chicco83/CHIRON-EVO/CHIRON/MOD HARDWARE/Anycubic_Trigorilla_stepper_driver_cooling_tunnel/images/3d06d213e04ff6a96ca5a01eb243599f_preview_featured.jpg

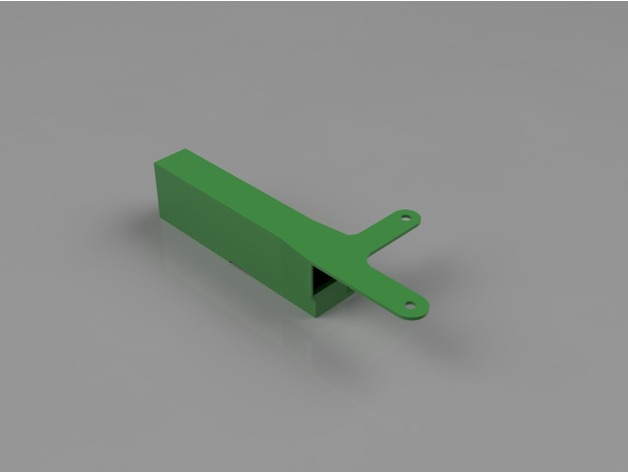
CHIRON/MOD HARDWARE/Anycubic_Trigorilla_stepper_driver_cooling_tunnel/images/3d06d213e04ff6a96ca5a01eb243599f_preview_featured.jpg
