chicco83/CHIRON-EVO/CHIRON/MOD HARDWARE/Anycubic_Trigorilla_stepper_driver_cooling_tunnel/images/8a05004b01cabfccfdbc358d301da0ce_preview_featured.jpg

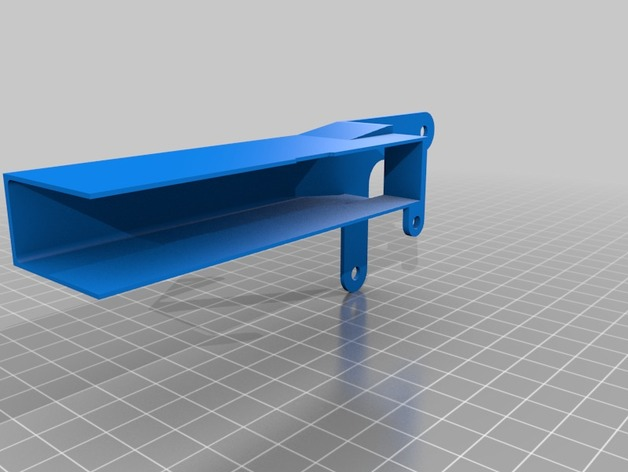
CHIRON/MOD HARDWARE/Anycubic_Trigorilla_stepper_driver_cooling_tunnel/images/8a05004b01cabfccfdbc358d301da0ce_preview_featured.jpg
