chicco83/CHIRON-EVO/CHIRON/MOD HARDWARE/Anycubic_Trigorilla_stepper_driver_cooling_tunnel/images/15cb524d84b9f957b413cb026b615ea2_preview_featured.jpg

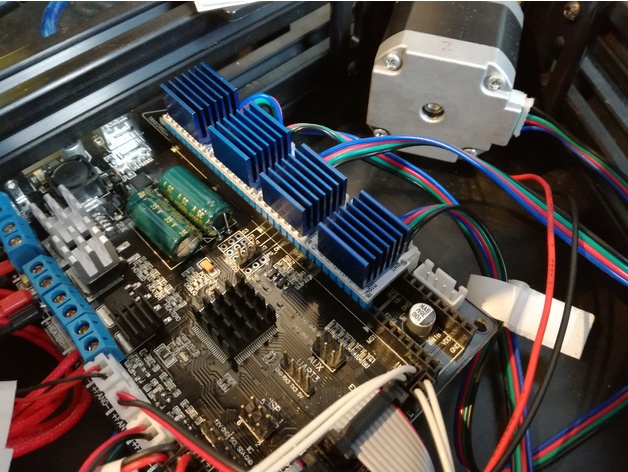
CHIRON/MOD HARDWARE/Anycubic_Trigorilla_stepper_driver_cooling_tunnel/images/15cb524d84b9f957b413cb026b615ea2_preview_featured.jpg
