chicco83/CHIRON-EVO/CHIRON/MOD HARDWARE/Anycubic_Trigorilla_stepper_driver_cooling_tunnel/images/66a94cb5b75e74bb501bde0653936604_preview_featured.jpg

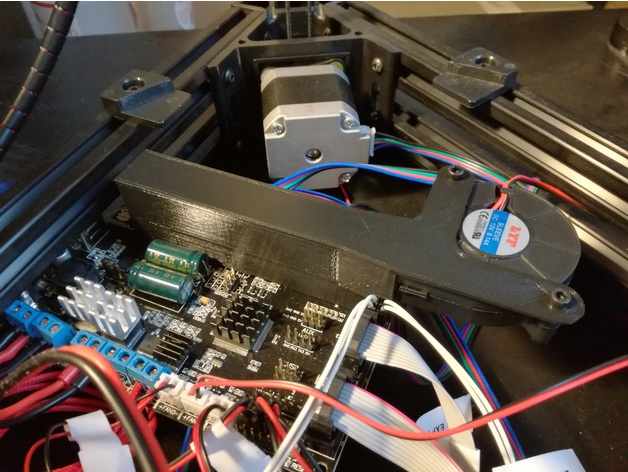
CHIRON/MOD HARDWARE/Anycubic_Trigorilla_stepper_driver_cooling_tunnel/images/66a94cb5b75e74bb501bde0653936604_preview_featured.jpg
