chicco83/CHIRON-EVO/CHIRON/MOD HARDWARE/Anycubic_Trigorilla_stepper_driver_cooling_tunnel/images/ea7234caf57d9d8a31c44bf39c441c15_preview_featured.jpg

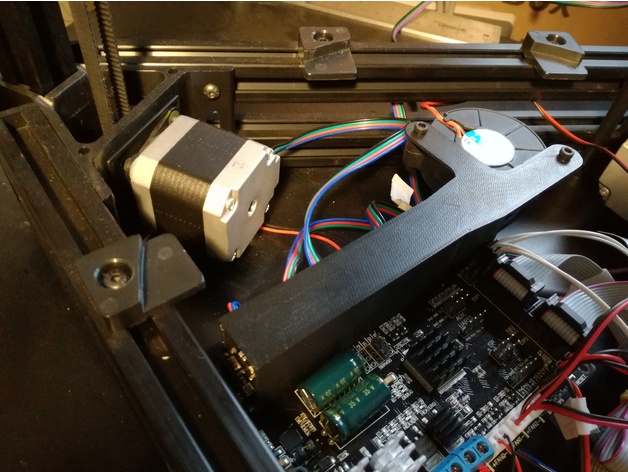
CHIRON/MOD HARDWARE/Anycubic_Trigorilla_stepper_driver_cooling_tunnel/images/ea7234caf57d9d8a31c44bf39c441c15_preview_featured.jpg
