chicco83/CHIRON-EVO/CHIRON/MOD HARDWARE/Anycubic_Trigorilla_stepper_driver_cooling_tunnel/images/ef3686a6fdcb9c2ef37c34229aa68580_preview_featured.jpg

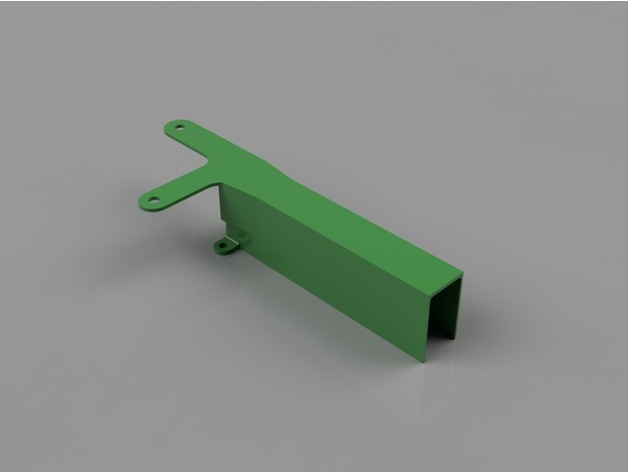
CHIRON/MOD HARDWARE/Anycubic_Trigorilla_stepper_driver_cooling_tunnel/images/ef3686a6fdcb9c2ef37c34229aa68580_preview_featured.jpg
