chicco83/CHIRON-EVO/CHIRON/MOD HARDWARE/Anycubic_Trigorilla_stepper_driver_cooling_tunnel/images/f9e21edd439fd3e9c4fc6578d0b51568_preview_featured.jpg

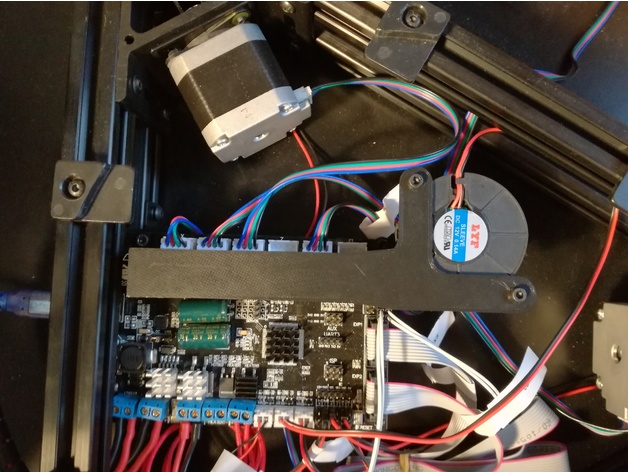
CHIRON/MOD HARDWARE/Anycubic_Trigorilla_stepper_driver_cooling_tunnel/images/f9e21edd439fd3e9c4fc6578d0b51568_preview_featured.jpg
