chicco83/CHIRON-EVO/CHIRON/MOD HARDWARE/PANNELLO PULSANTI/Octoprint+Buttonbox+/files/IMG_20211204_123243.jpg

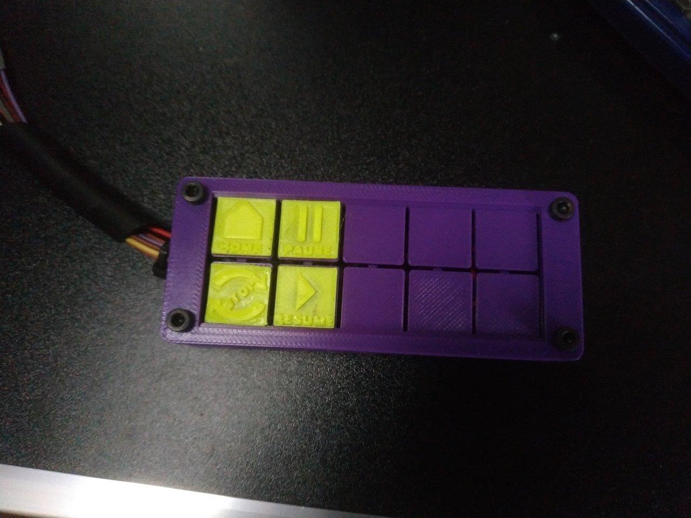
CHIRON/MOD HARDWARE/PANNELLO PULSANTI/Octoprint+Buttonbox+/files/IMG_20211204_123243.jpg
