chicco83/CHIRON-EVO/CHIRON/MOD HARDWARE/PANNELLO PULSANTI/Octoprint+Buttonbox+/images/20200816_074949-2.jpg

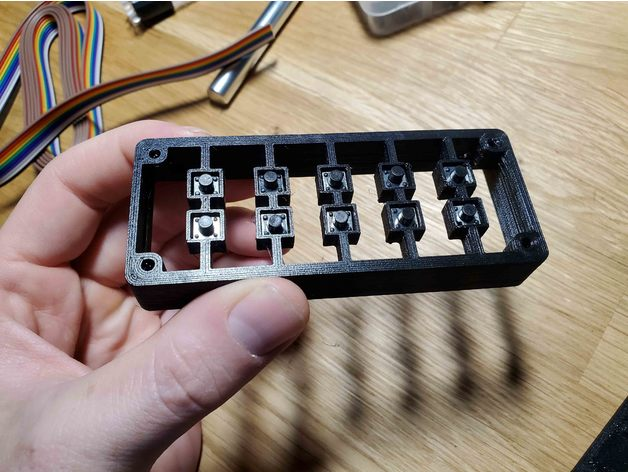
CHIRON/MOD HARDWARE/PANNELLO PULSANTI/Octoprint+Buttonbox+/images/20200816_074949-2.jpg
