chicco83/CHIRON-EVO/CHIRON/MOD HARDWARE/PANNELLO PULSANTI/Octoprint+Buttonbox+/images/20200816_090715.jpg

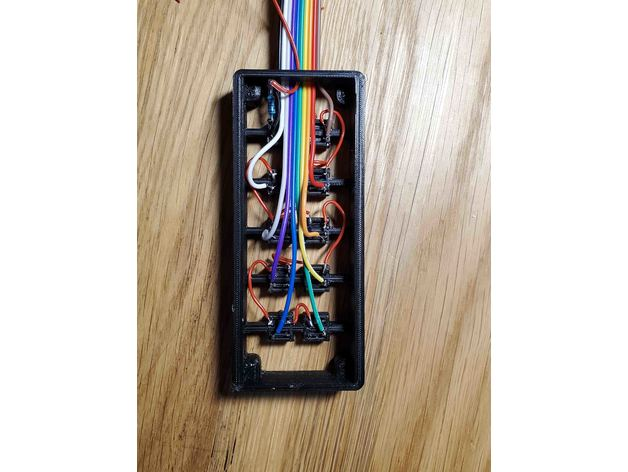
CHIRON/MOD HARDWARE/PANNELLO PULSANTI/Octoprint+Buttonbox+/images/20200816_090715.jpg
