chicco83/CHIRON-EVO/CHIRON/MOD HARDWARE/pinout cavo nero.jpg

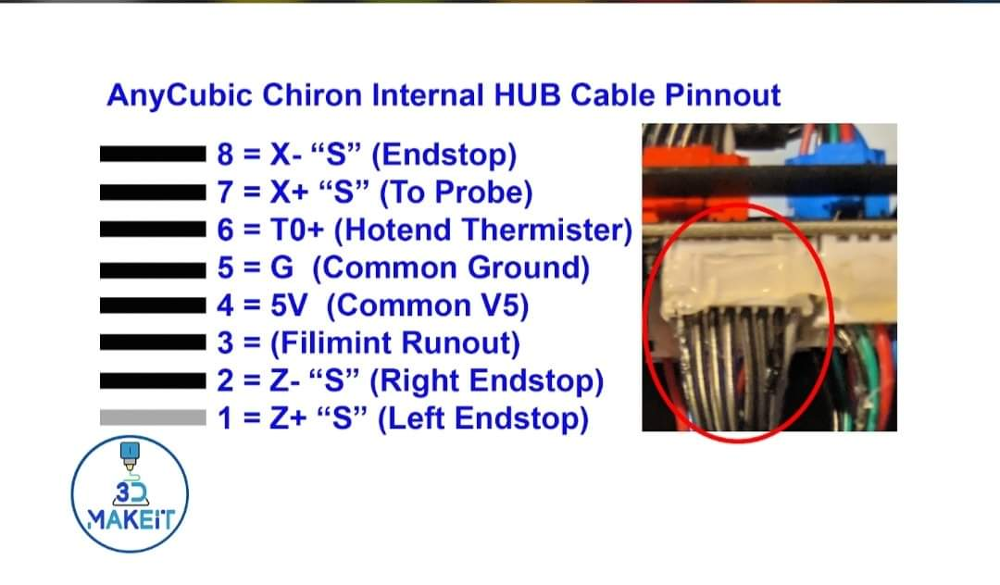
CHIRON/MOD HARDWARE/pinout cavo nero.jpg
