chicco83/CHIRON-EVO/CHIRON/MOD HARDWARE/PINOUT CONNETTORE ROSSO ESTRUSORE.jpg

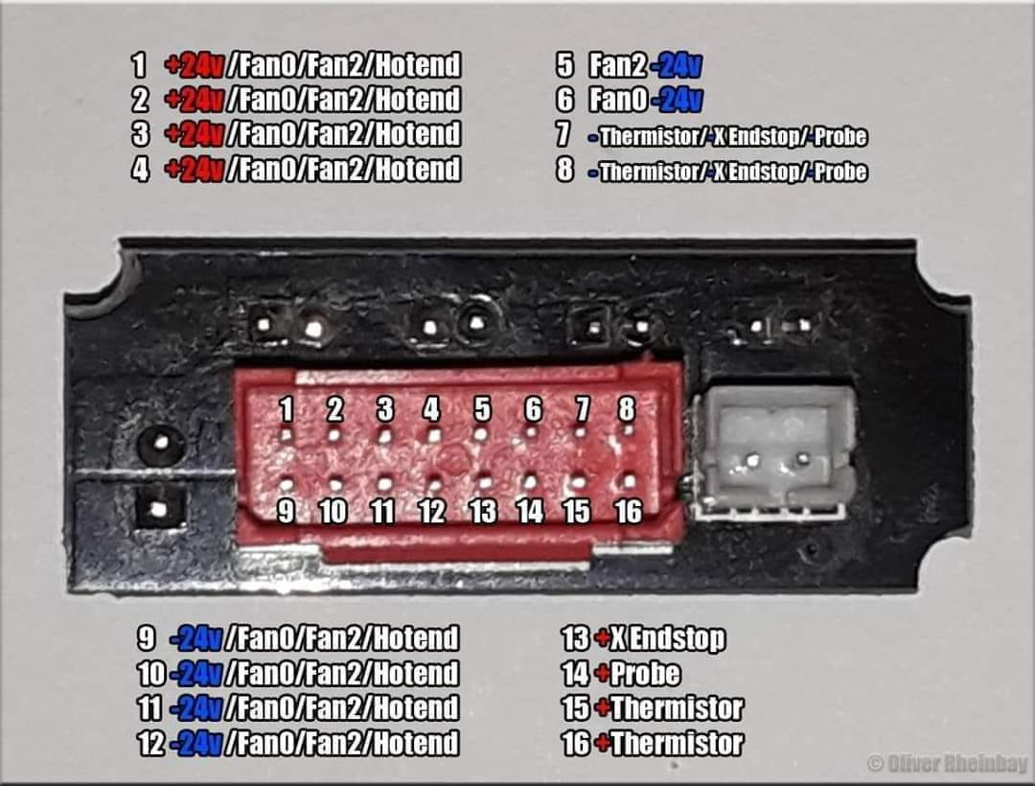
CHIRON/MOD HARDWARE/PINOUT CONNETTORE ROSSO ESTRUSORE.jpg
