chicco83/CHIRON-EVO/CHIRON/MOD HARDWARE/Supporto Stabilizzante Chiron/Images/Componente top Chiron.PNG

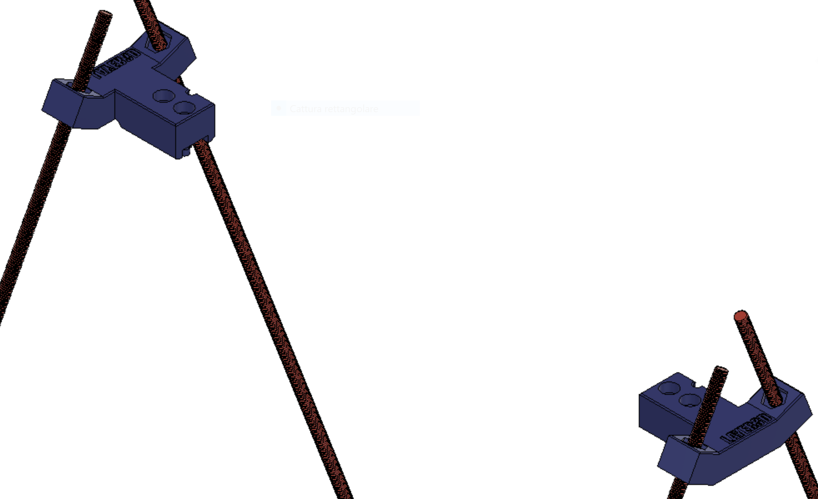
CHIRON/MOD HARDWARE/Supporto Stabilizzante Chiron/Images/Componente top Chiron.PNG
