chicco83/CHIRON-EVO/CHIRON/MOD HARDWARE/Supporto Stabilizzante Chiron/Images/Piedi scarico tensioni Z Chiron.PNG

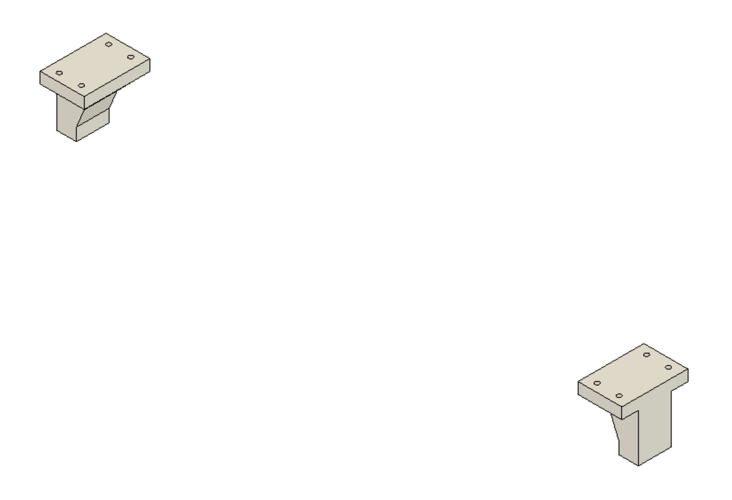
CHIRON/MOD HARDWARE/Supporto Stabilizzante Chiron/Images/Piedi scarico tensioni Z Chiron.PNG
