chicco83/CHIRON-EVO/CHIRON/MOD HARDWARE/Supporto Stabilizzante Chiron/Images/Rinforzo asse y Chiron.PNG

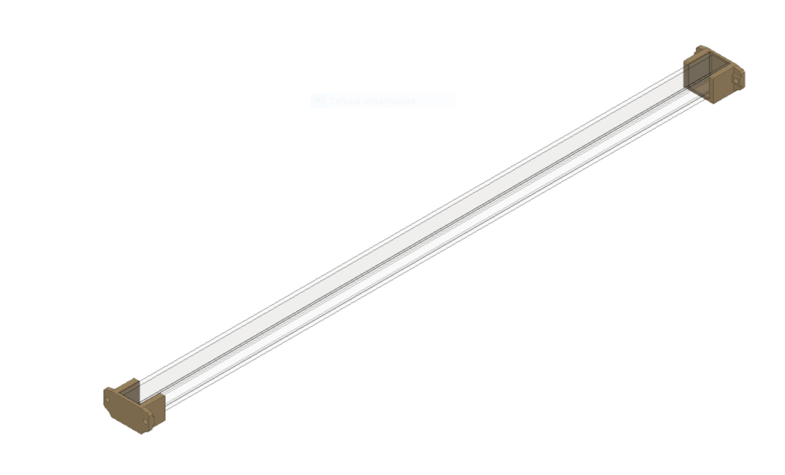
CHIRON/MOD HARDWARE/Supporto Stabilizzante Chiron/Images/Rinforzo asse y Chiron.PNG
