chicco83/CHIRON-EVO/CHIRON/MOD HARDWARE/trigorilla_motherboard_pinout.jpg

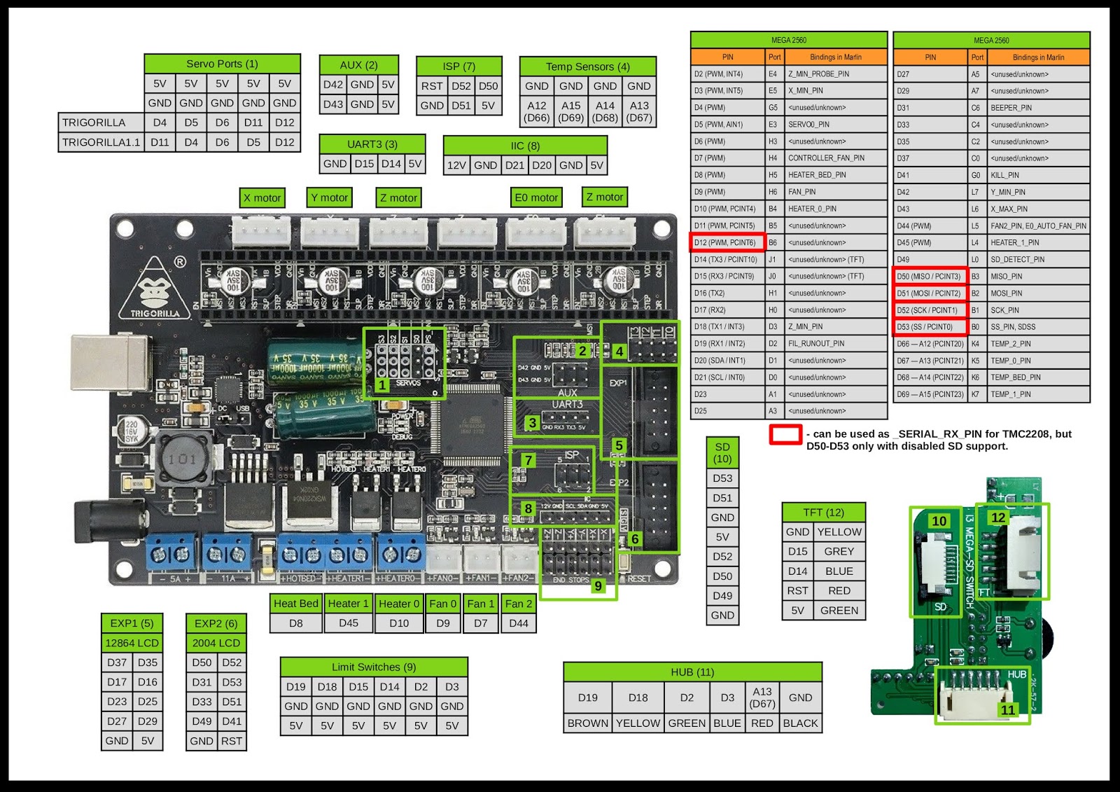
CHIRON/MOD HARDWARE/trigorilla_motherboard_pinout.jpg
