chicco83/CHIRON-EVO/CHIRON/SUPERSLICER/CHIRON BED.png

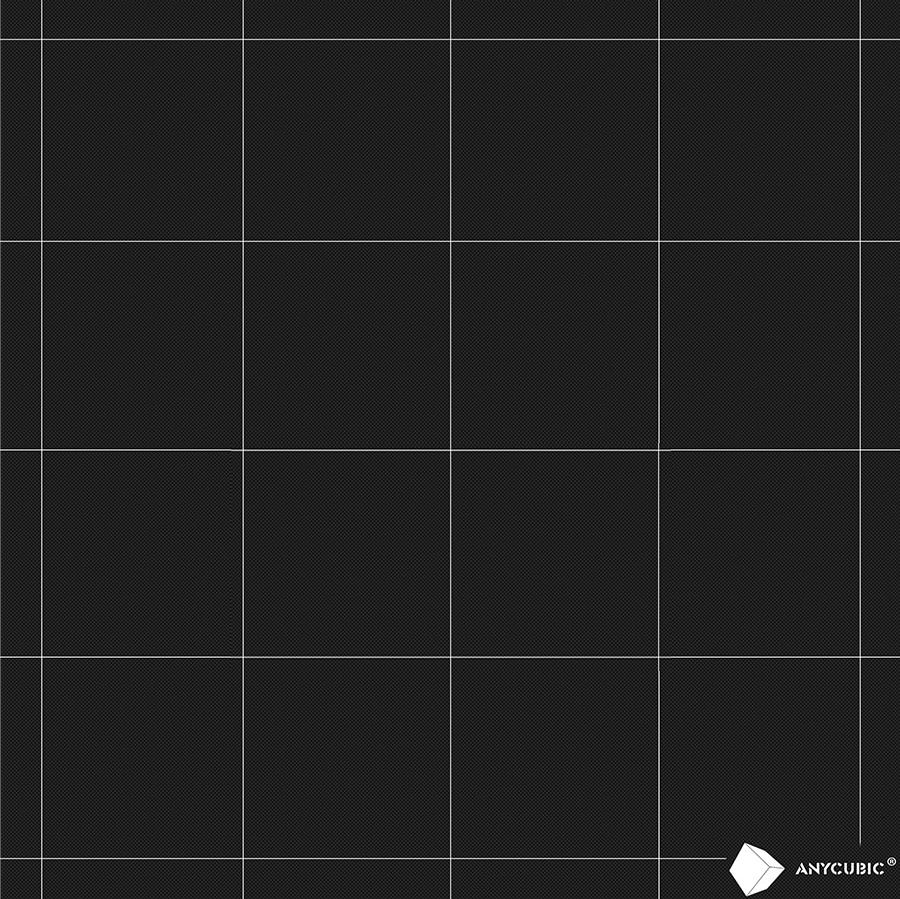
CHIRON/SUPERSLICER/CHIRON BED.png
