chicco83/CHIRON-EVO/CHIRON/VREF/Anycubic Chiron Vrefs.png

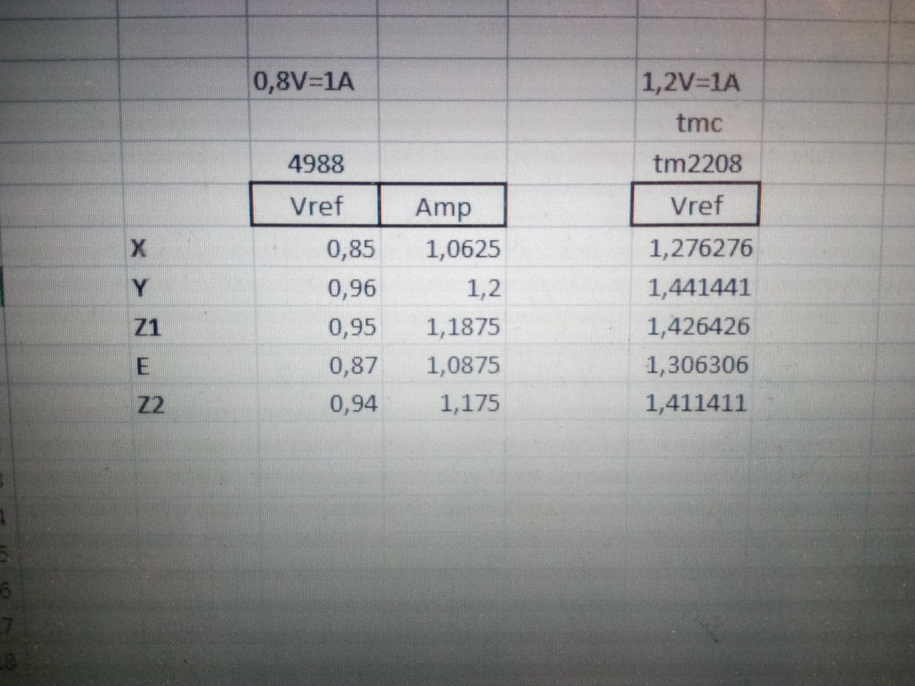
CHIRON/VREF/Anycubic Chiron Vrefs.png
