chicco83/CHIRON-EVO/CHIRON/VREF/vref anycubic - credit gruppo fb chiron italia/FB_IMG_1618653829422.jpg

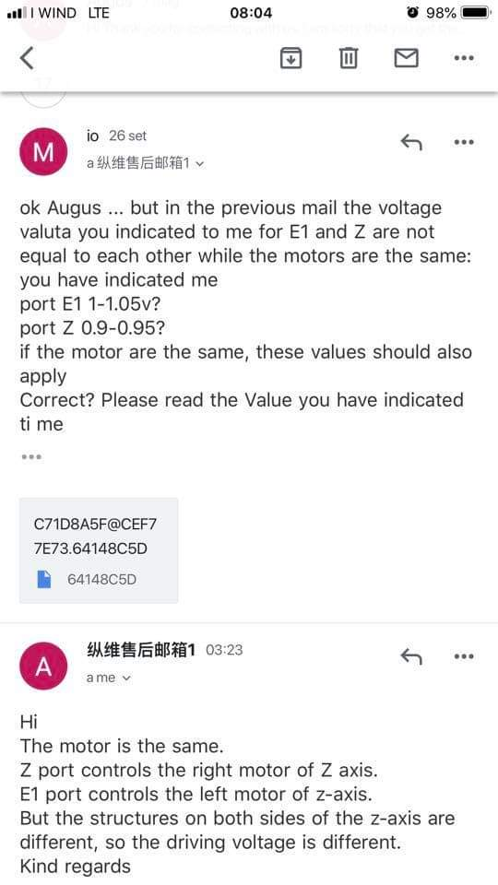
CHIRON/VREF/vref anycubic - credit gruppo fb chiron italia/FB_IMG_1618653829422.jpg
