chicco83/CHIRON-EVO/KLIPPER/DA STAMPARE/5v relay case/images/5V_relay_v2.jpg

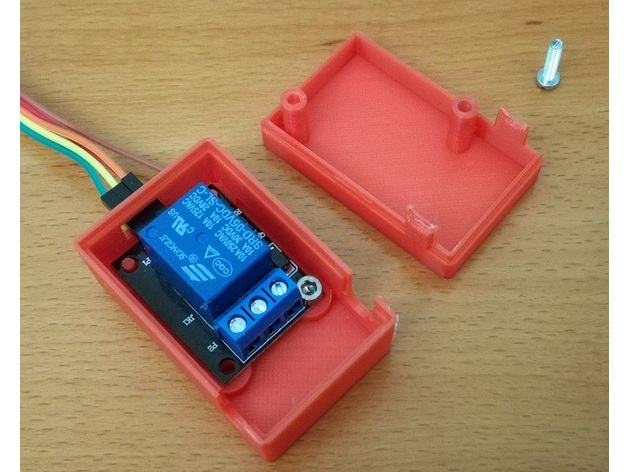
KLIPPER/DA STAMPARE/5v relay case/images/5V_relay_v2.jpg
