chicco83/CHIRON-EVO/KLIPPER/DA STAMPARE/5v relay case/images/extension_cord.jpg

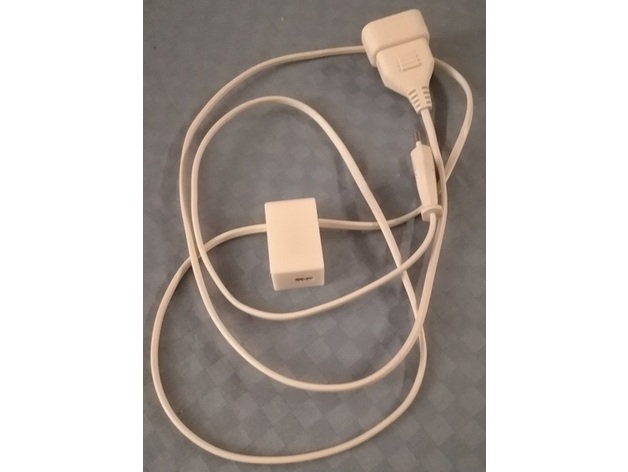
KLIPPER/DA STAMPARE/5v relay case/images/extension_cord.jpg
