chicco83/CHIRON-EVO/KLIPPER/DA STAMPARE/5v relay case/images/Parameters.jpg

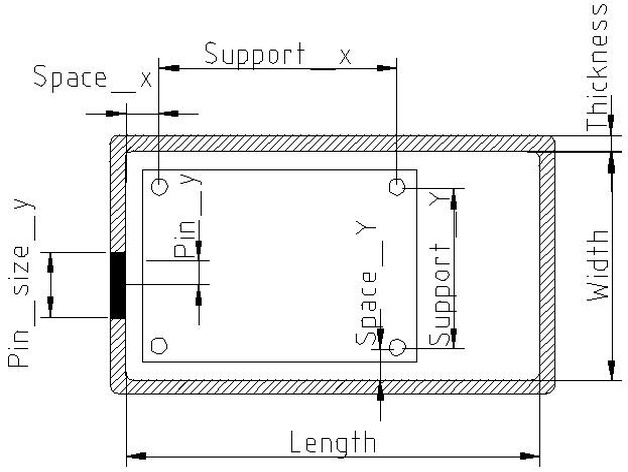
KLIPPER/DA STAMPARE/5v relay case/images/Parameters.jpg
