chicco83/CHIRON-EVO/KLIPPER/DA STAMPARE/Raspberry_Pi_3_B_Case/images/2fc77e1b27ac55f75d19a529d03621bc_preview_featured.jpg

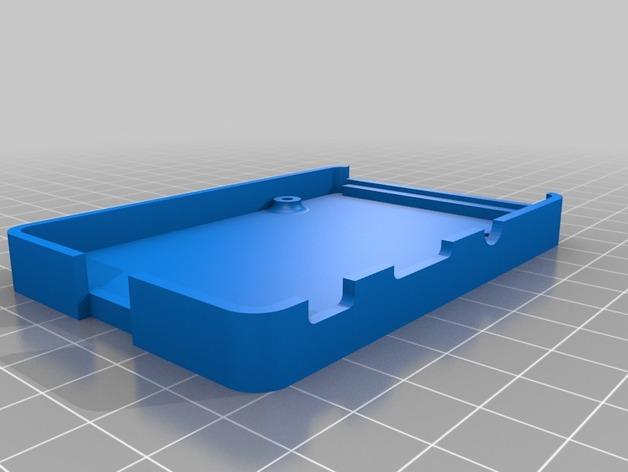
KLIPPER/DA STAMPARE/Raspberry_Pi_3_B_Case/images/2fc77e1b27ac55f75d19a529d03621bc_preview_featured.jpg
