chicco83/CHIRON-EVO/KLIPPER/DA STAMPARE/Raspberry_Pi_3_B_Case/images/3aaac6f96571e5535b9cd6b619069dd5_preview_featured.jpg

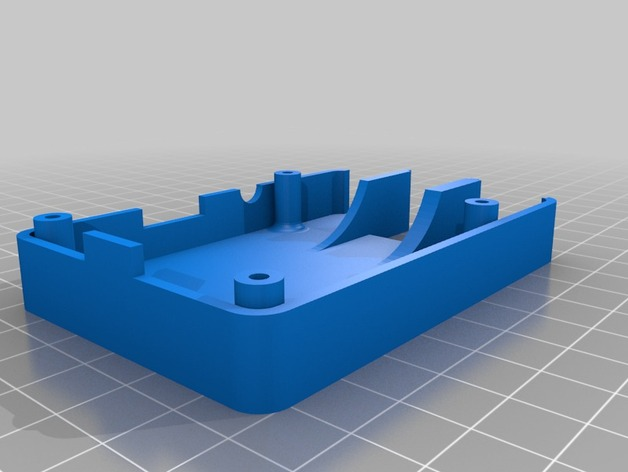
KLIPPER/DA STAMPARE/Raspberry_Pi_3_B_Case/images/3aaac6f96571e5535b9cd6b619069dd5_preview_featured.jpg
