chicco83/CHIRON-EVO/KLIPPER/DA STAMPARE/Raspberry_Pi_3_B_Case/images/6a6be3c9e7a6a9a813ffc517b591dac2_preview_featured.JPG

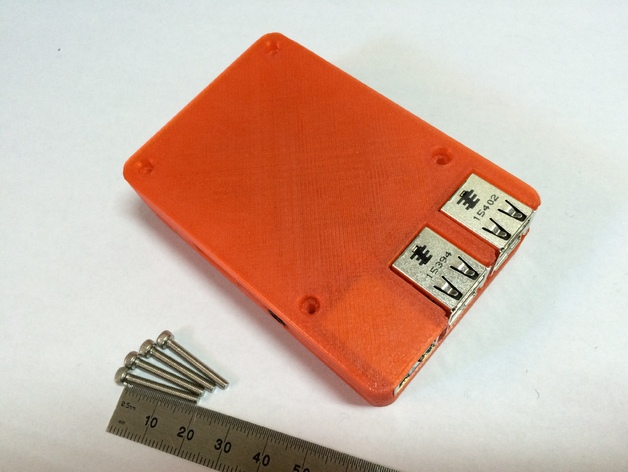
KLIPPER/DA STAMPARE/Raspberry_Pi_3_B_Case/images/6a6be3c9e7a6a9a813ffc517b591dac2_preview_featured.JPG
