chicco83/CHIRON-EVO/KLIPPER/DA STAMPARE/Raspberry_Pi_3_B_Case/images/39cf647c955a4db6509a8b4bb3a802ad_preview_featured.JPG

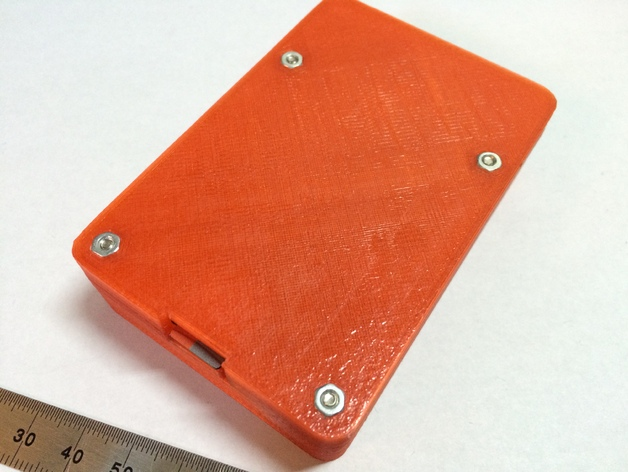
KLIPPER/DA STAMPARE/Raspberry_Pi_3_B_Case/images/39cf647c955a4db6509a8b4bb3a802ad_preview_featured.JPG
