chicco83/CHIRON-EVO/KLIPPER/DA STAMPARE/Raspberry_Pi_3_B_Case/images/99bb187c00068765ed25da04c6e93b3f_preview_featured.JPG

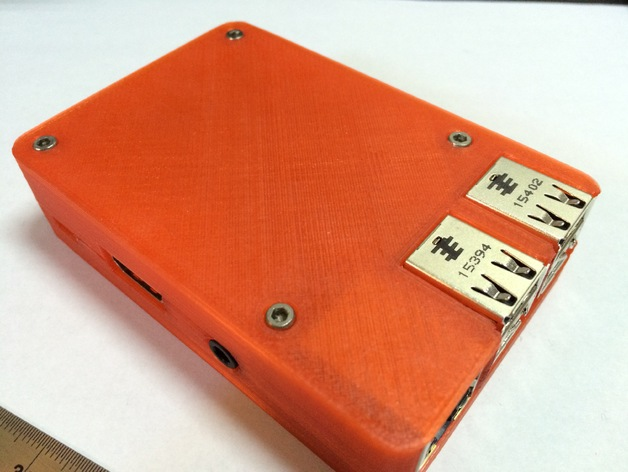
KLIPPER/DA STAMPARE/Raspberry_Pi_3_B_Case/images/99bb187c00068765ed25da04c6e93b3f_preview_featured.JPG
