chicco83/CHIRON-EVO/KLIPPER/DA STAMPARE/Raspberry_Pi_3_B_Case/images/a91bb46b5abf62a84486f4e04251a870_preview_featured.jpg

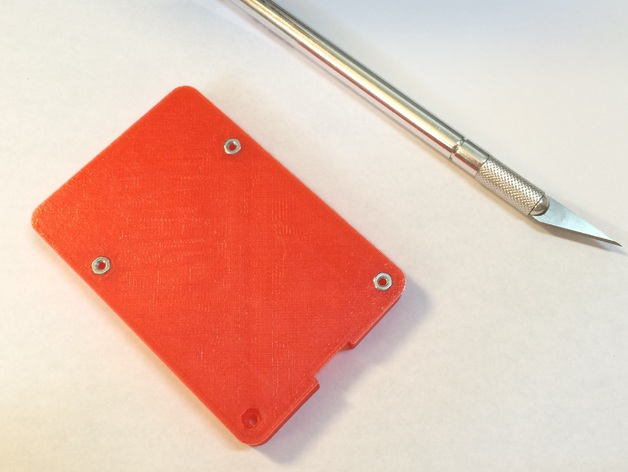
KLIPPER/DA STAMPARE/Raspberry_Pi_3_B_Case/images/a91bb46b5abf62a84486f4e04251a870_preview_featured.jpg
