chicco83/CHIRON-EVO/KLIPPER/DA STAMPARE/Raspberry_Pi_3_B_Case/images/a355228bfaae16f2a482a3d36976ca95_preview_featured.jpg

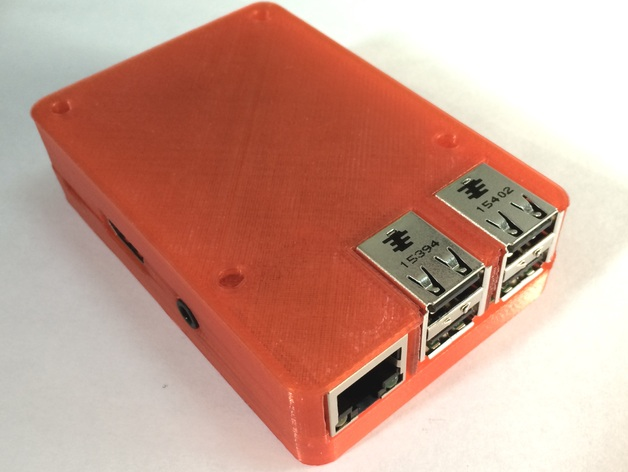
KLIPPER/DA STAMPARE/Raspberry_Pi_3_B_Case/images/a355228bfaae16f2a482a3d36976ca95_preview_featured.jpg
