chicco83/CHIRON-EVO/KLIPPER/DA STAMPARE/Raspberry_Pi_3_B_Case/images/ac6876f8ac2d007c6f56735a2c74a32b_preview_featured.jpg

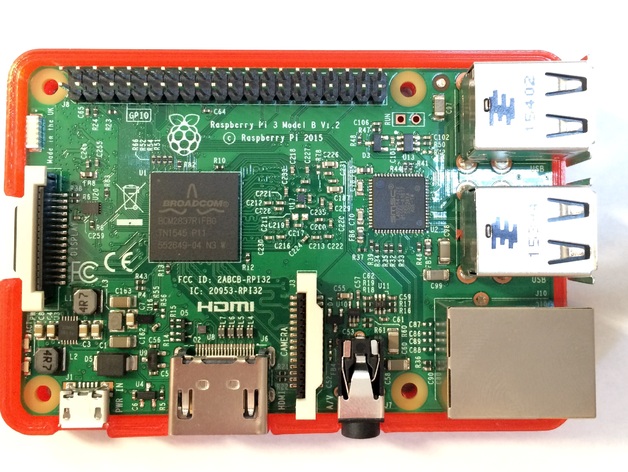
KLIPPER/DA STAMPARE/Raspberry_Pi_3_B_Case/images/ac6876f8ac2d007c6f56735a2c74a32b_preview_featured.jpg
