chicco83/CHIRON-EVO/KLIPPER/DA STAMPARE/Raspberry_Pi_3_B_Case/images/f00792783482409bf88fcd65ae3375f5_preview_featured.jpg

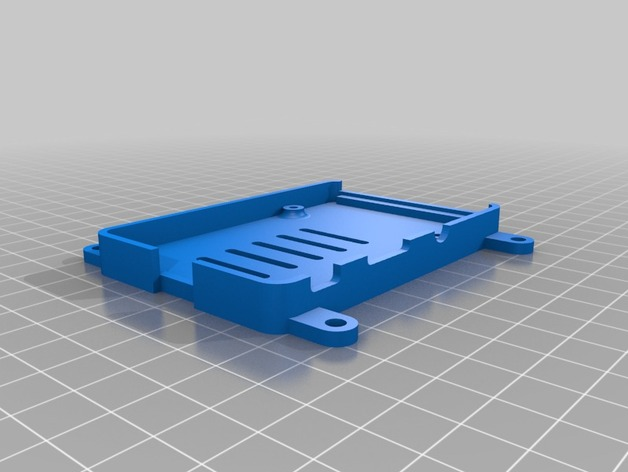
KLIPPER/DA STAMPARE/Raspberry_Pi_3_B_Case/images/f00792783482409bf88fcd65ae3375f5_preview_featured.jpg
