chicco83/CHIRON-EVO/TARATURE/Calibration cube.3mf

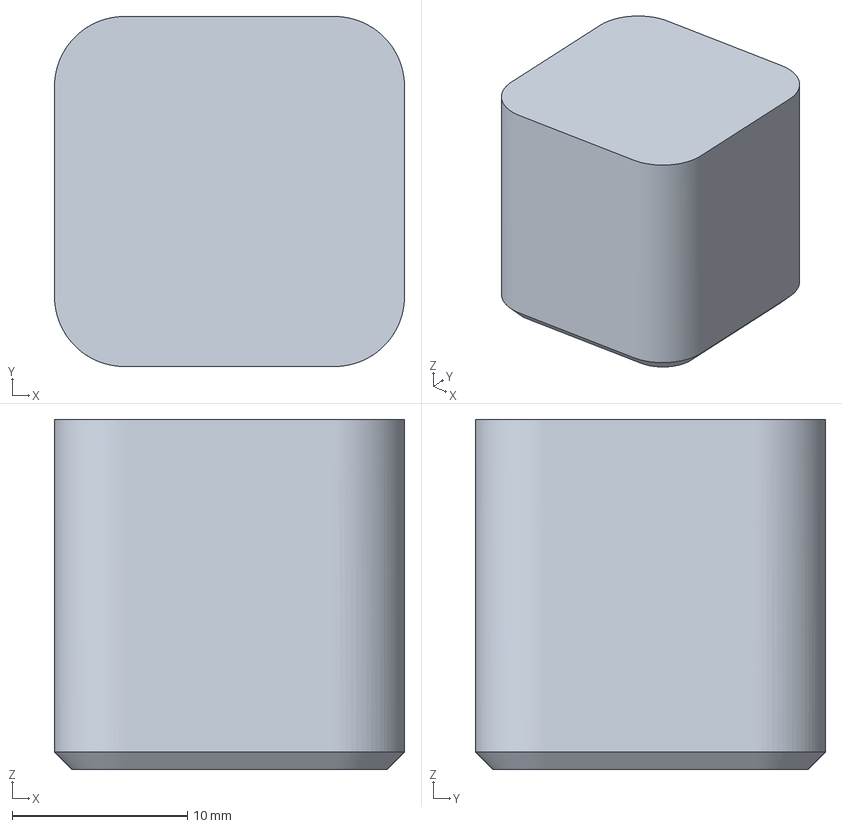
[picture p59: CAD file, 2021-11-13]
TARATURE/Calibration cube.3mf
20.0 x 20.0 x 20.0 mm
