chicco83/CHIRON-EVO/CHIRON/MOD HARDWARE/PANNELLO PULSANTI/Octoprint+Buttonbox+/files/button_base_v2.stl

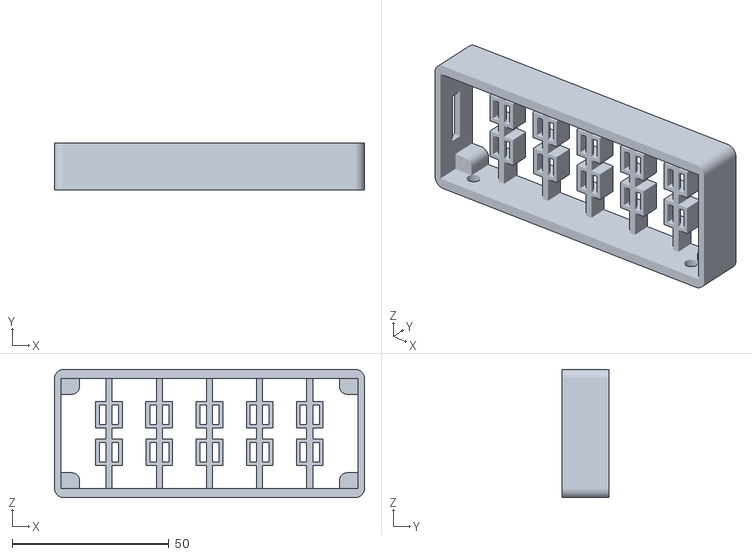
[picture p60: CAD file, 2021-11-13]
CHIRON/MOD HARDWARE/PANNELLO PULSANTI/Octoprint+Buttonbox+/files/button_base_v2.stl
99.0 x 15.0 x 41.0
