chicco83/CHIRON-EVO/CHIRON/MOD HARDWARE/Supporto Stabilizzante Chiron/Files/fatti/Piede dx  Z Chiron.3mf

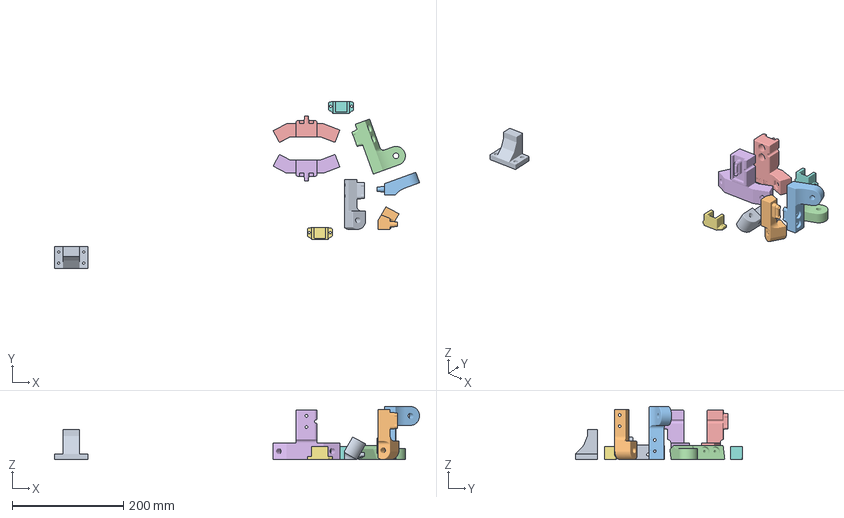
[picture p61: CAD file, 2021-04-02]
CHIRON/MOD HARDWARE/Supporto Stabilizzante Chiron/Files/fatti/Piede dx Z Chiron.3mf
656.4 x 301.1 x 95.4 mm
Supporto anteriore barra M10 dx Chiron.stl
Supporto anteriore barra M10 sx Chiron.stl
Supporto posteriore barra M10 dx Chiron.stl
Supporto posteriore barra M10 sx Chiron.stl
Componente top dx Z Chiron.stl
Componente top sx Z Chiron.stl
Rinforzo asse y scatolato 2020 anteriore Chiron.stl
Rinforzo asse y scatolato 2020 posteriore Chiron.stl
Piede dx Z Chiron.stl
