chicco83/CHIRON-EVO/KLIPPER/DA STAMPARE/Raspberry_Pi_3_B_Case/files/Pi3_Top_Honeycomb.3mf

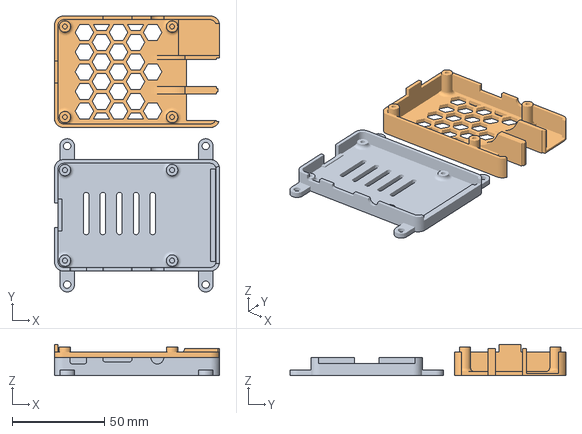
[picture p62: CAD file, 2021-04-02]
KLIPPER/DA STAMPARE/Raspberry_Pi_3_B_Case/files/Pi3_Top_Honeycomb.3mf
89.4 x 149.4 x 17.1 mm
Pi3_Bottom_VESA.stl
Pi3_Top_Honeycomb.stl
