chicco83/CHIRON-EVO/KLIPPER/DA STAMPARE/supporto tab 7/clip8mmMore.stl

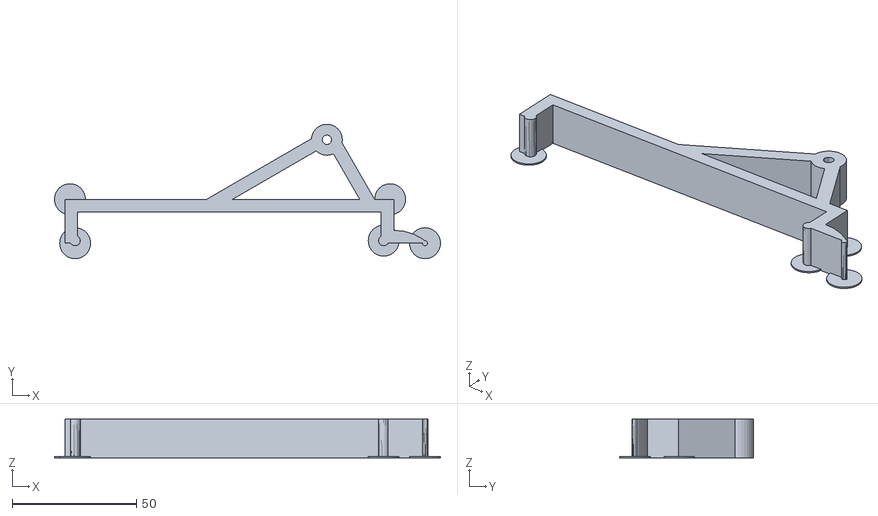
[picture p63: CAD file, 2021-04-02]
KLIPPER/DA STAMPARE/supporto tab 7/clip8mmMore.stl
155.5 x 54.2 x 15.6
