chicco83/CHIRON-EVO/CHIRON/MOD HARDWARE/PANNELLO PULSANTI/Octoprint+Buttonbox+/files/button_box_.step

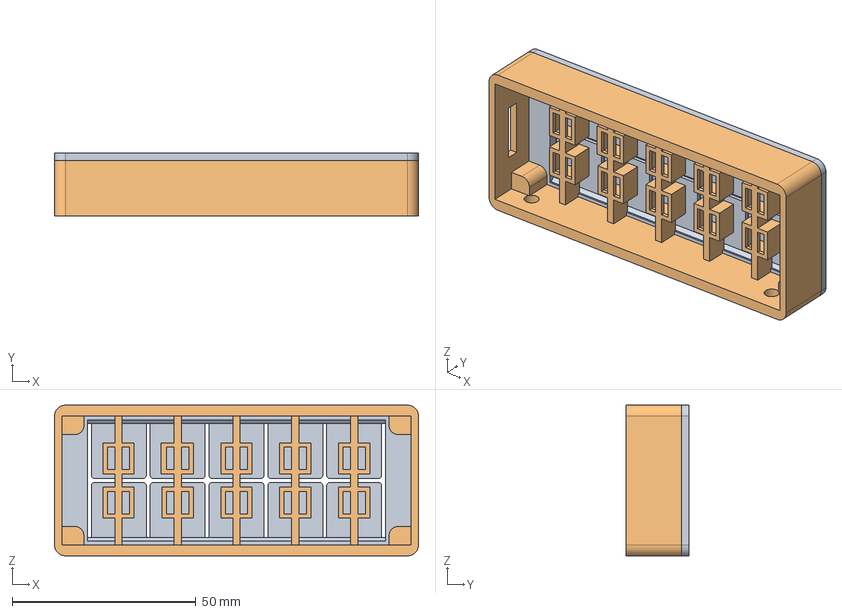
[picture p64: CAD file, 2021-11-13]
CHIRON/MOD HARDWARE/PANNELLO PULSANTI/Octoprint+Buttonbox+/files/button_box_.step
99.0 x 17.0 x 41.0 mm
buttonpad
