chicco83/CHIRON-EVO/KLIPPER/DA STAMPARE/Raspberry_Pi_3_B_Case/files/Pi3_Top_40mm_Fan.stl

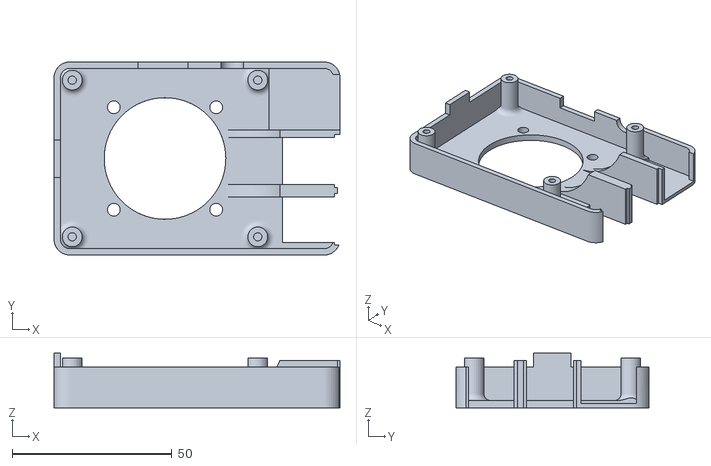
[picture p65: CAD file, 2021-04-02]
KLIPPER/DA STAMPARE/Raspberry_Pi_3_B_Case/files/Pi3_Top_40mm_Fan.stl
89.4 x 60.4 x 17.1
