chicco83/CHIRON-EVO/KLIPPER/DA STAMPARE/supporto tab 7/arm.stl

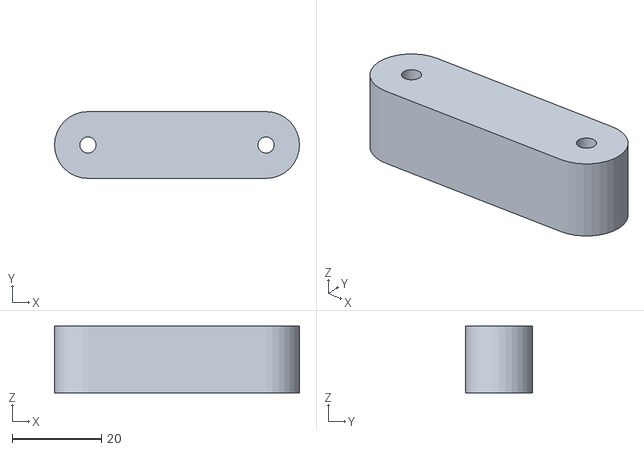
[picture p66: CAD file, 2021-04-02]
KLIPPER/DA STAMPARE/supporto tab 7/arm.stl
55.0 x 15.0 x 15.0
