chicco83/CHIRON-EVO/CHIRON/MOD HARDWARE/PANNELLO PULSANTI/Octoprint+Buttonbox+/files/BUTTONS.3mf

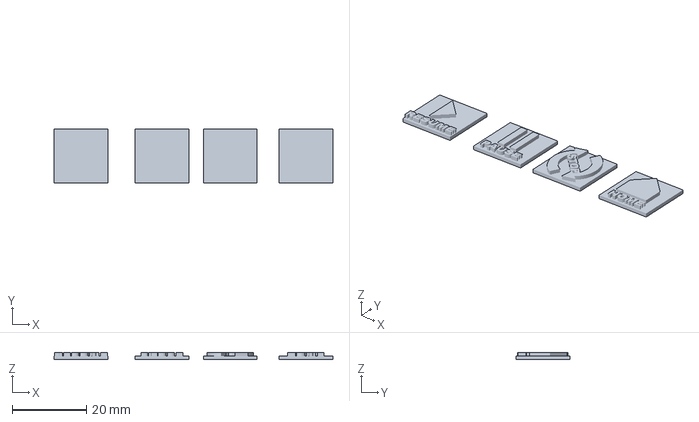
[picture p67: CAD file, 2021-11-13]
CHIRON/MOD HARDWARE/PANNELLO PULSANTI/Octoprint+Buttonbox+/files/BUTTONS.3mf
75.0 x 14.5 x 2.00 mm
