chicco83/CHIRON-EVO/KLIPPER/DA STAMPARE/Raspberry_Pi_3_B_Case/files/Pi3_Bottom_VESA.stl

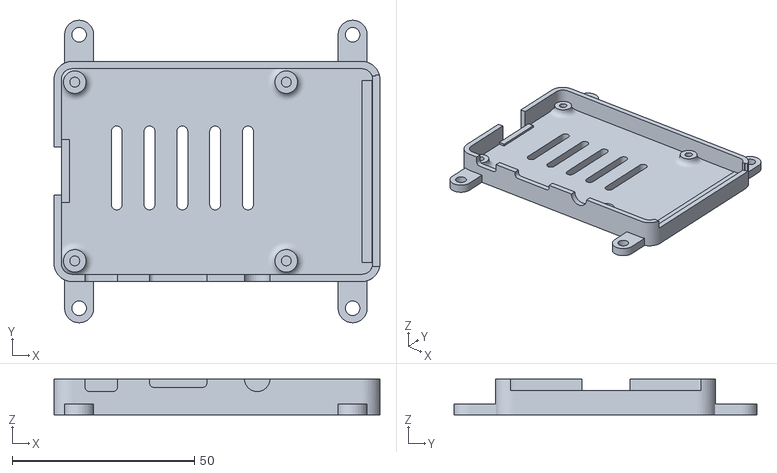
[picture p68: CAD file, 2021-04-02]
KLIPPER/DA STAMPARE/Raspberry_Pi_3_B_Case/files/Pi3_Bottom_VESA.stl
89.4 x 83.0 x 9.75
