chicco83/CHIRON-EVO/KLIPPER/DA STAMPARE/supporto tab 7/supporto tab.3mf

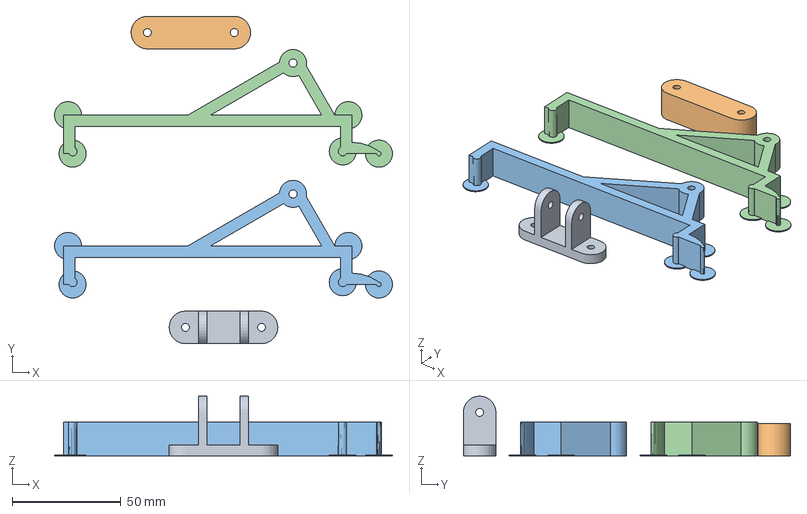
[picture p69: CAD file, 2021-04-02]
KLIPPER/DA STAMPARE/supporto tab 7/supporto tab.3mf
155.5 x 150.6 x 27.5 mm
mount.stl
arm.stl
clip8mmMore.stl
