chicco83/CHIRON-EVO/KLIPPER/DA STAMPARE/Raspberry_Pi_3_B_Case/files/Pi3_Bottom_Vents.stl

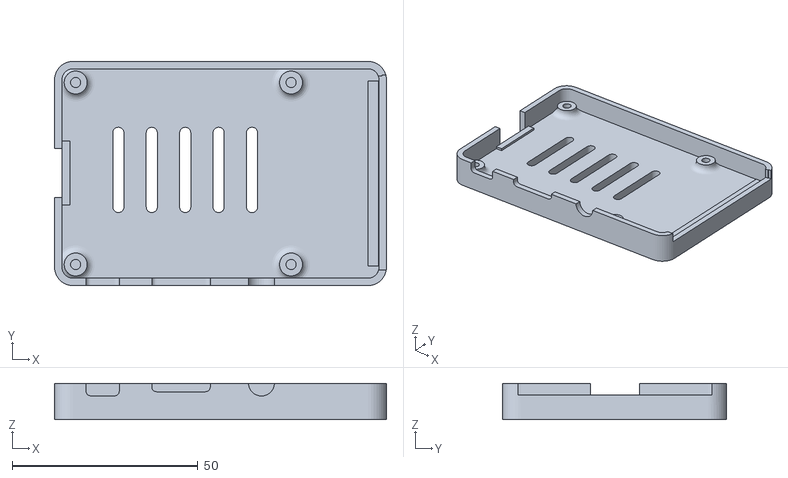
[picture p70: CAD file, 2021-04-02]
KLIPPER/DA STAMPARE/Raspberry_Pi_3_B_Case/files/Pi3_Bottom_Vents.stl
89.4 x 60.4 x 9.75
