chicco83/CHIRON-EVO/CHIRON/MOD HARDWARE/Supporto Stabilizzante Chiron/Files/fatti/Componente top sx Z Chiron.3mf

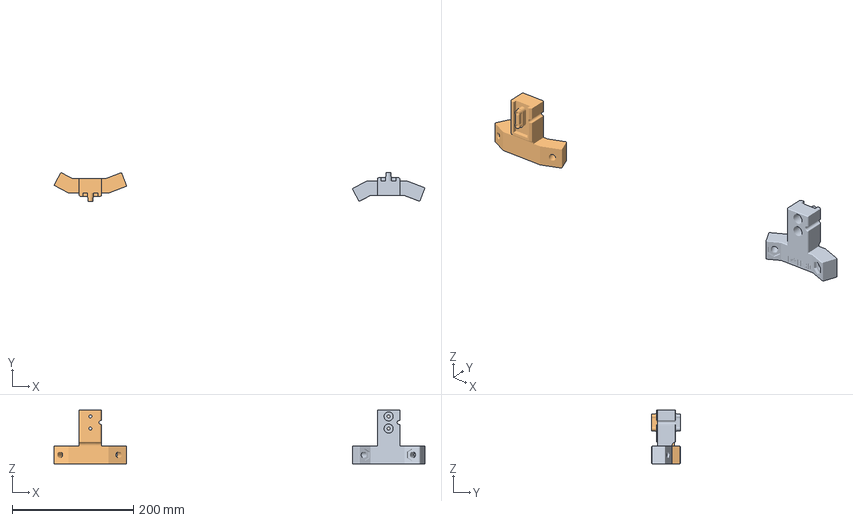
[picture p71: CAD file, 2021-04-02]
CHIRON/MOD HARDWARE/Supporto Stabilizzante Chiron/Files/fatti/Componente top sx Z Chiron.3mf
612.0 x 47.1 x 88.9 mm
Componente top dx Z Chiron.stl
Componente top sx Z Chiron.stl
