chicco83/CHIRON-EVO/CHIRON/MOD HARDWARE/Supporto Stabilizzante Chiron/Files/fatti/Supporto posteriore barra M10 sx Chiron.stl

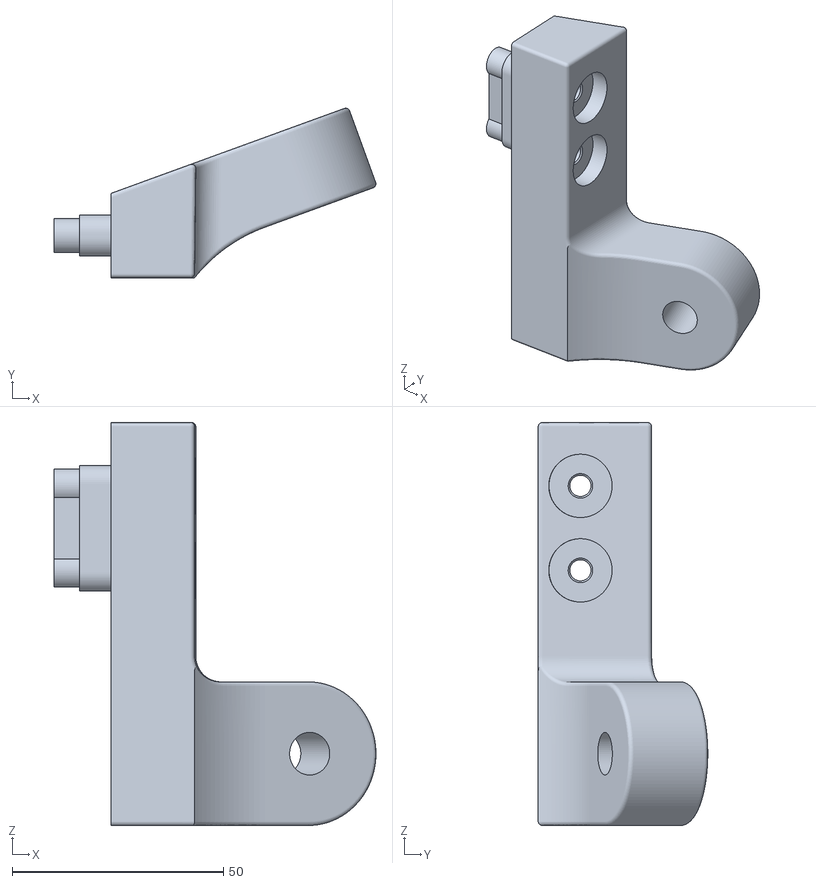
[picture p72: CAD file, 2021-04-02]
CHIRON/MOD HARDWARE/Supporto Stabilizzante Chiron/Files/fatti/Supporto posteriore barra M10 sx Chiron.stl
76.2 x 40.2 x 95.4
