chicco83/CHIRON-EVO/CHIRON/MOD HARDWARE/Supporto Stabilizzante Chiron/Files/fatti/Componente top dx Z Chiron.stl

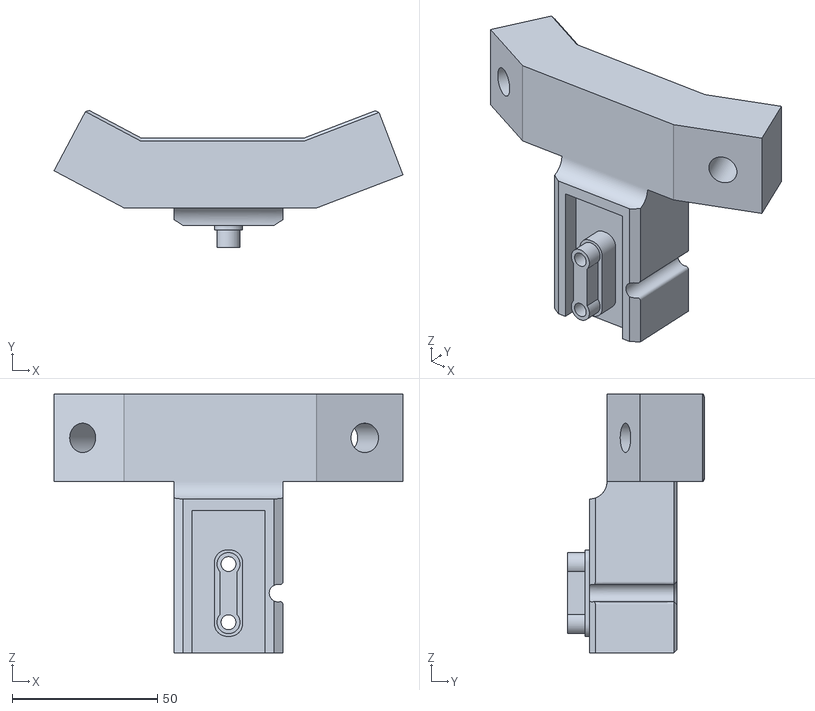
[picture p73: CAD file, 2021-04-02]
CHIRON/MOD HARDWARE/Supporto Stabilizzante Chiron/Files/fatti/Componente top dx Z Chiron.stl
120.0 x 47.1 x 88.9
