chicco83/CHIRON-EVO/CHIRON/MOD HARDWARE/Supporto Stabilizzante Chiron/Files/fatti/Rinforzo asse y scatolato 2020.3mf

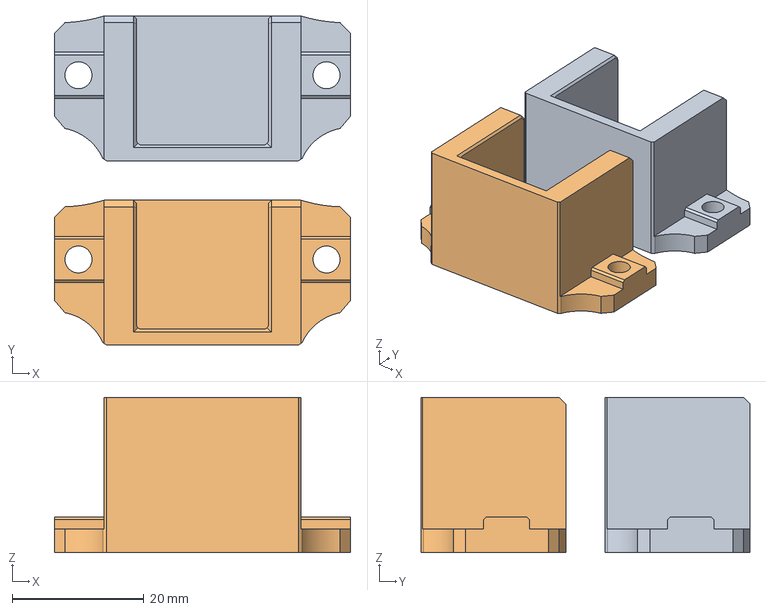
[picture p74: CAD file, 2021-04-02]
CHIRON/MOD HARDWARE/Supporto Stabilizzante Chiron/Files/fatti/Rinforzo asse y scatolato 2020.3mf
45.0 x 50.0 x 23.6 mm
Rinforzo asse y scatolato 2020 anteriore Chiron.stl
Rinforzo asse y scatolato 2020 posteriore Chiron.stl
