chicco83/CHIRON-EVO/CHIRON/MOD HARDWARE/Supporto Stabilizzante Chiron/Files/fatti/supporti inferiori barre M10.3mf

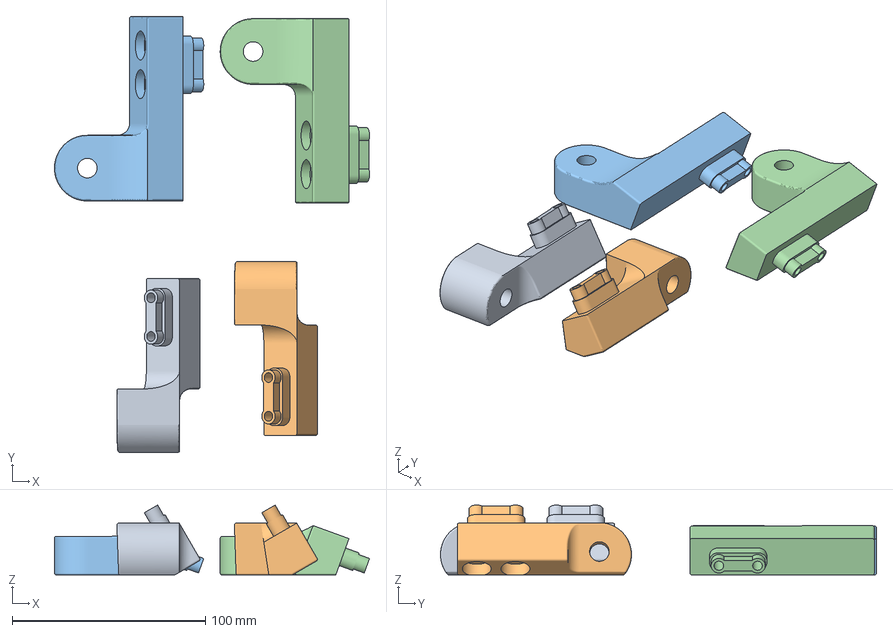
[picture p75: CAD file, 2021-04-02]
CHIRON/MOD HARDWARE/Supporto Stabilizzante Chiron/Files/fatti/supporti inferiori barre M10.3mf
162.9 x 225.4 x 36.2 mm
Supporto anteriore barra M10 dx Chiron.stl
Supporto anteriore barra M10 sx Chiron.stl
Supporto posteriore barra M10 dx Chiron.stl
Supporto posteriore barra M10 sx Chiron.stl
