chicco83/CHIRON-EVO/CHIRON/MOD HARDWARE/Chiron+Fan+Duct+Shorter+for+better+print+clearance/images/0849F4FE-72D7-40BB-91F6-A561DE7557D7.jpeg

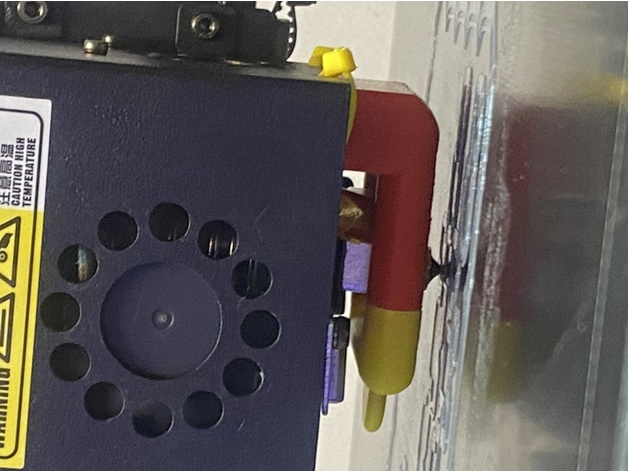
CHIRON/MOD HARDWARE/Chiron+Fan+Duct+Shorter+for+better+print+clearance/images/0849F4FE-72D7-40BB-91F6-A561DE7557D7.jpeg
