chicco83/CHIRON-EVO/CHIRON/MOD HARDWARE/Chiron+Fan+Duct+Shorter+for+better+print+clearance/images/Chiron_Fanduct_Larger_Vents_End_Cap.png

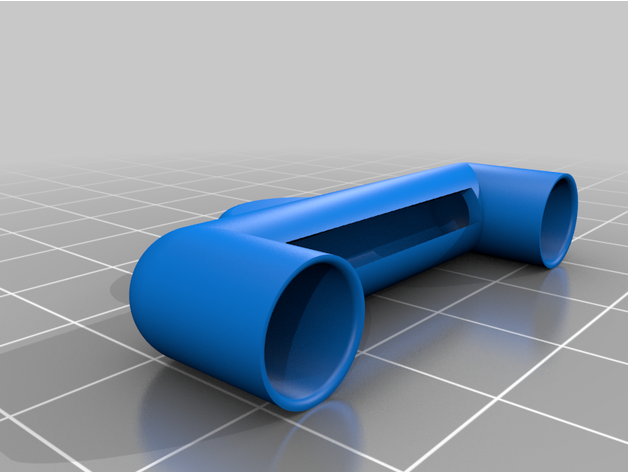
CHIRON/MOD HARDWARE/Chiron+Fan+Duct+Shorter+for+better+print+clearance/images/Chiron_Fanduct_Larger_Vents_End_Cap.png
