chicco83/CHIRON-EVO/CHIRON/MOD HARDWARE/Chiron_X_stepper_cover_with_cable_guide/images/3ea8b5d324f198f5a6011591848cc464_preview_featured.jpg

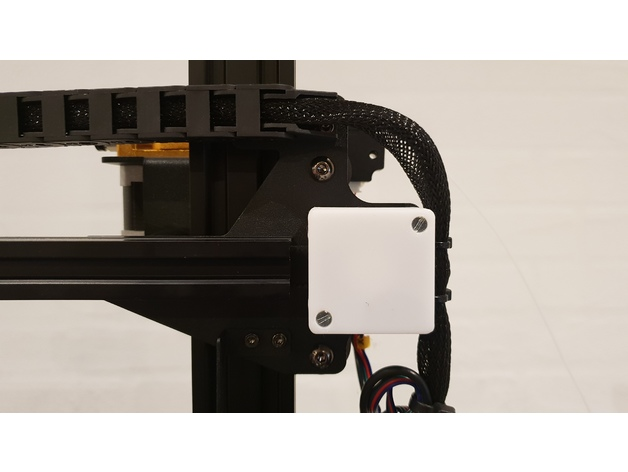
CHIRON/MOD HARDWARE/Chiron_X_stepper_cover_with_cable_guide/images/3ea8b5d324f198f5a6011591848cc464_preview_featured.jpg
