chicco83/CHIRON-EVO/CHIRON/MOD HARDWARE/Chiron_X_stepper_cover_with_cable_guide/images/795ec2c78adedfa42bc923c354108f1b_preview_featured.jpg

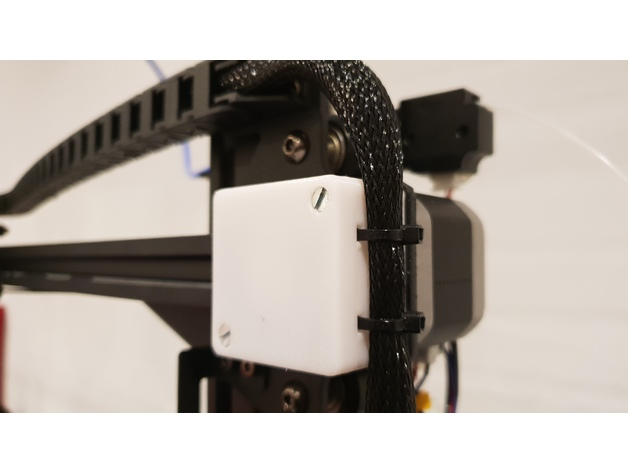
CHIRON/MOD HARDWARE/Chiron_X_stepper_cover_with_cable_guide/images/795ec2c78adedfa42bc923c354108f1b_preview_featured.jpg
