chicco83/CHIRON-EVO/CHIRON/MOD HARDWARE/Chiron_X_stepper_cover_with_cable_guide/images/b71077100a22c80ae4d427c0fc774e7c_preview_featured.jpg

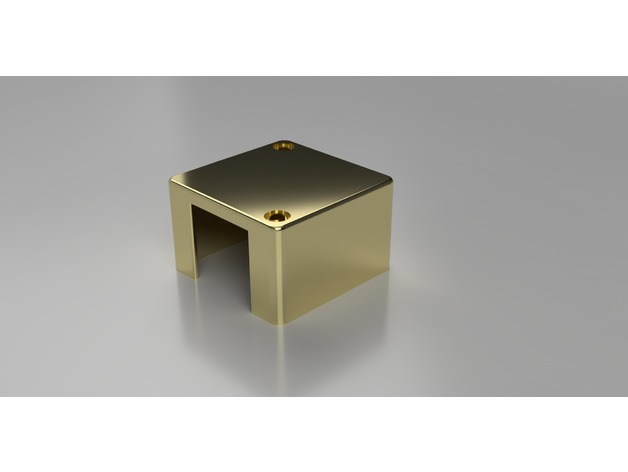
CHIRON/MOD HARDWARE/Chiron_X_stepper_cover_with_cable_guide/images/b71077100a22c80ae4d427c0fc774e7c_preview_featured.jpg
