chicco83/CHIRON-EVO/CHIRON/MOD HARDWARE/Chiron_X_stepper_cover_with_cable_guide/images/bc4ea90938d82dec1ddc9f6f187a3dae_preview_featured.jpg

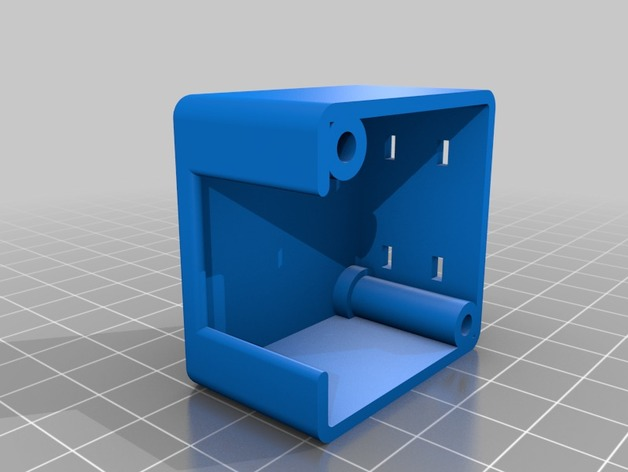
CHIRON/MOD HARDWARE/Chiron_X_stepper_cover_with_cable_guide/images/bc4ea90938d82dec1ddc9f6f187a3dae_preview_featured.jpg
