chicco83/CHIRON-EVO/CHIRON/MOD HARDWARE/Chiron_X_stepper_cover_with_cable_guide/images/ff4814ab1bfa7c12ce026915109dad45_preview_featured.jpg

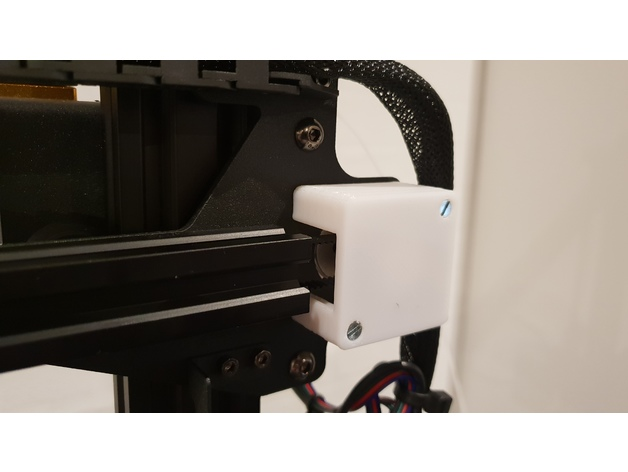
CHIRON/MOD HARDWARE/Chiron_X_stepper_cover_with_cable_guide/images/ff4814ab1bfa7c12ce026915109dad45_preview_featured.jpg
