chicco83/CHIRON-EVO/CHIRON/MOD HARDWARE/INSTALLAZIONE RELE/IMG_20210404_200111.jpg

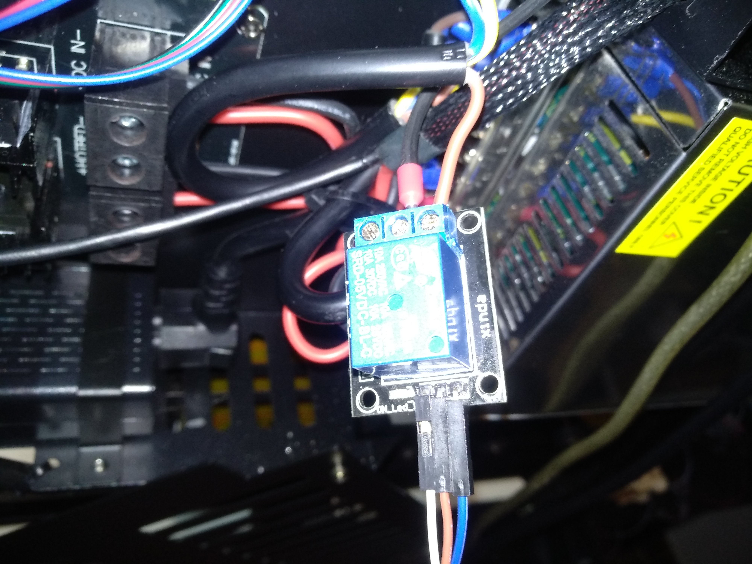
CHIRON/MOD HARDWARE/INSTALLAZIONE RELE/IMG_20210404_200111.jpg
