chicco83/CHIRON-EVO/CHIRON/MOD HARDWARE/fix porta t03 su mb 1.0/4K7_fehlt.jpg

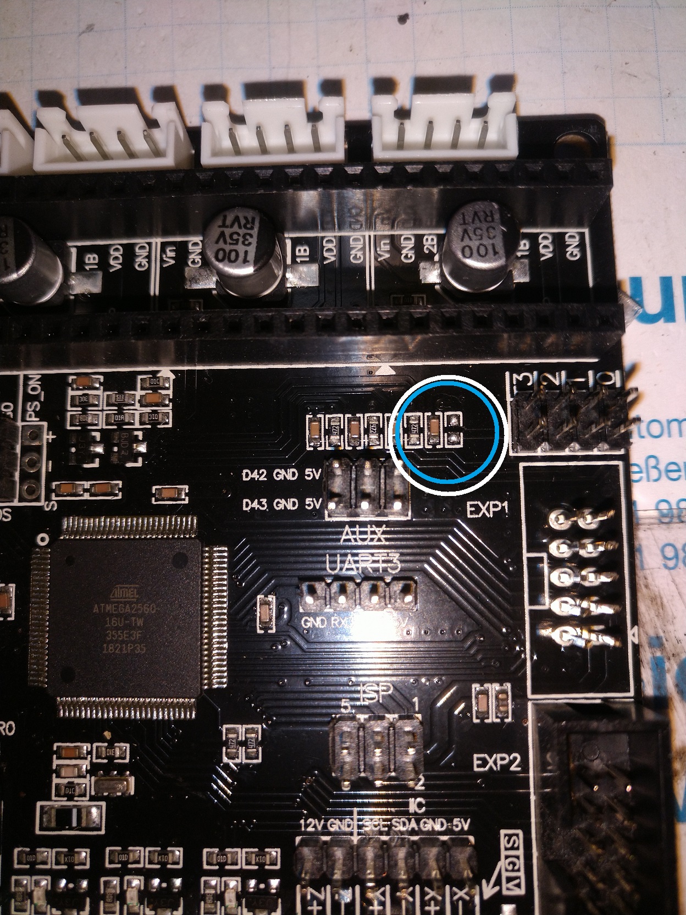
CHIRON/MOD HARDWARE/fix porta t03 su mb 1.0/4K7_fehlt.jpg
